layereight/nfc-music-box/images/01_pizerow.jpg

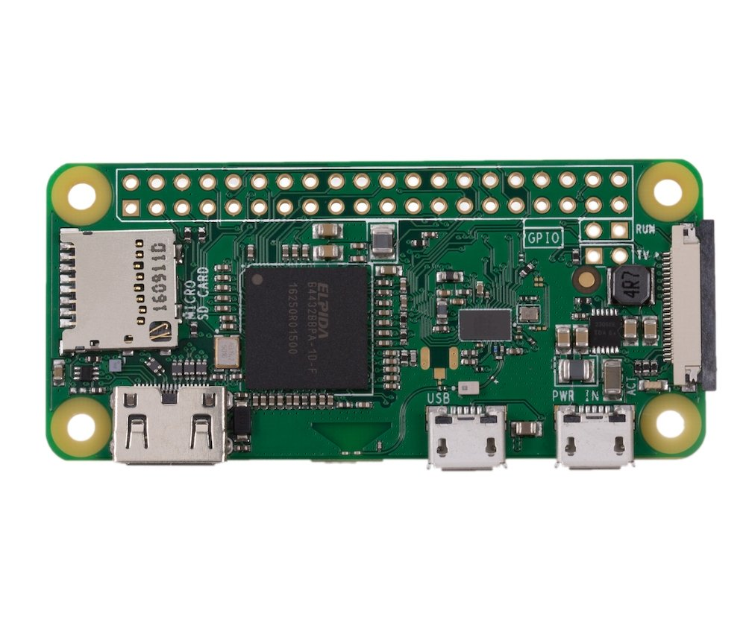
images/01_pizerow.jpg
